DynamicWhiteHat/Arc/CAD/PCB/Freedom.kicad_sch

## KiCad design CAD/PCB/Freedom.kicad_sch (2026-02-23)

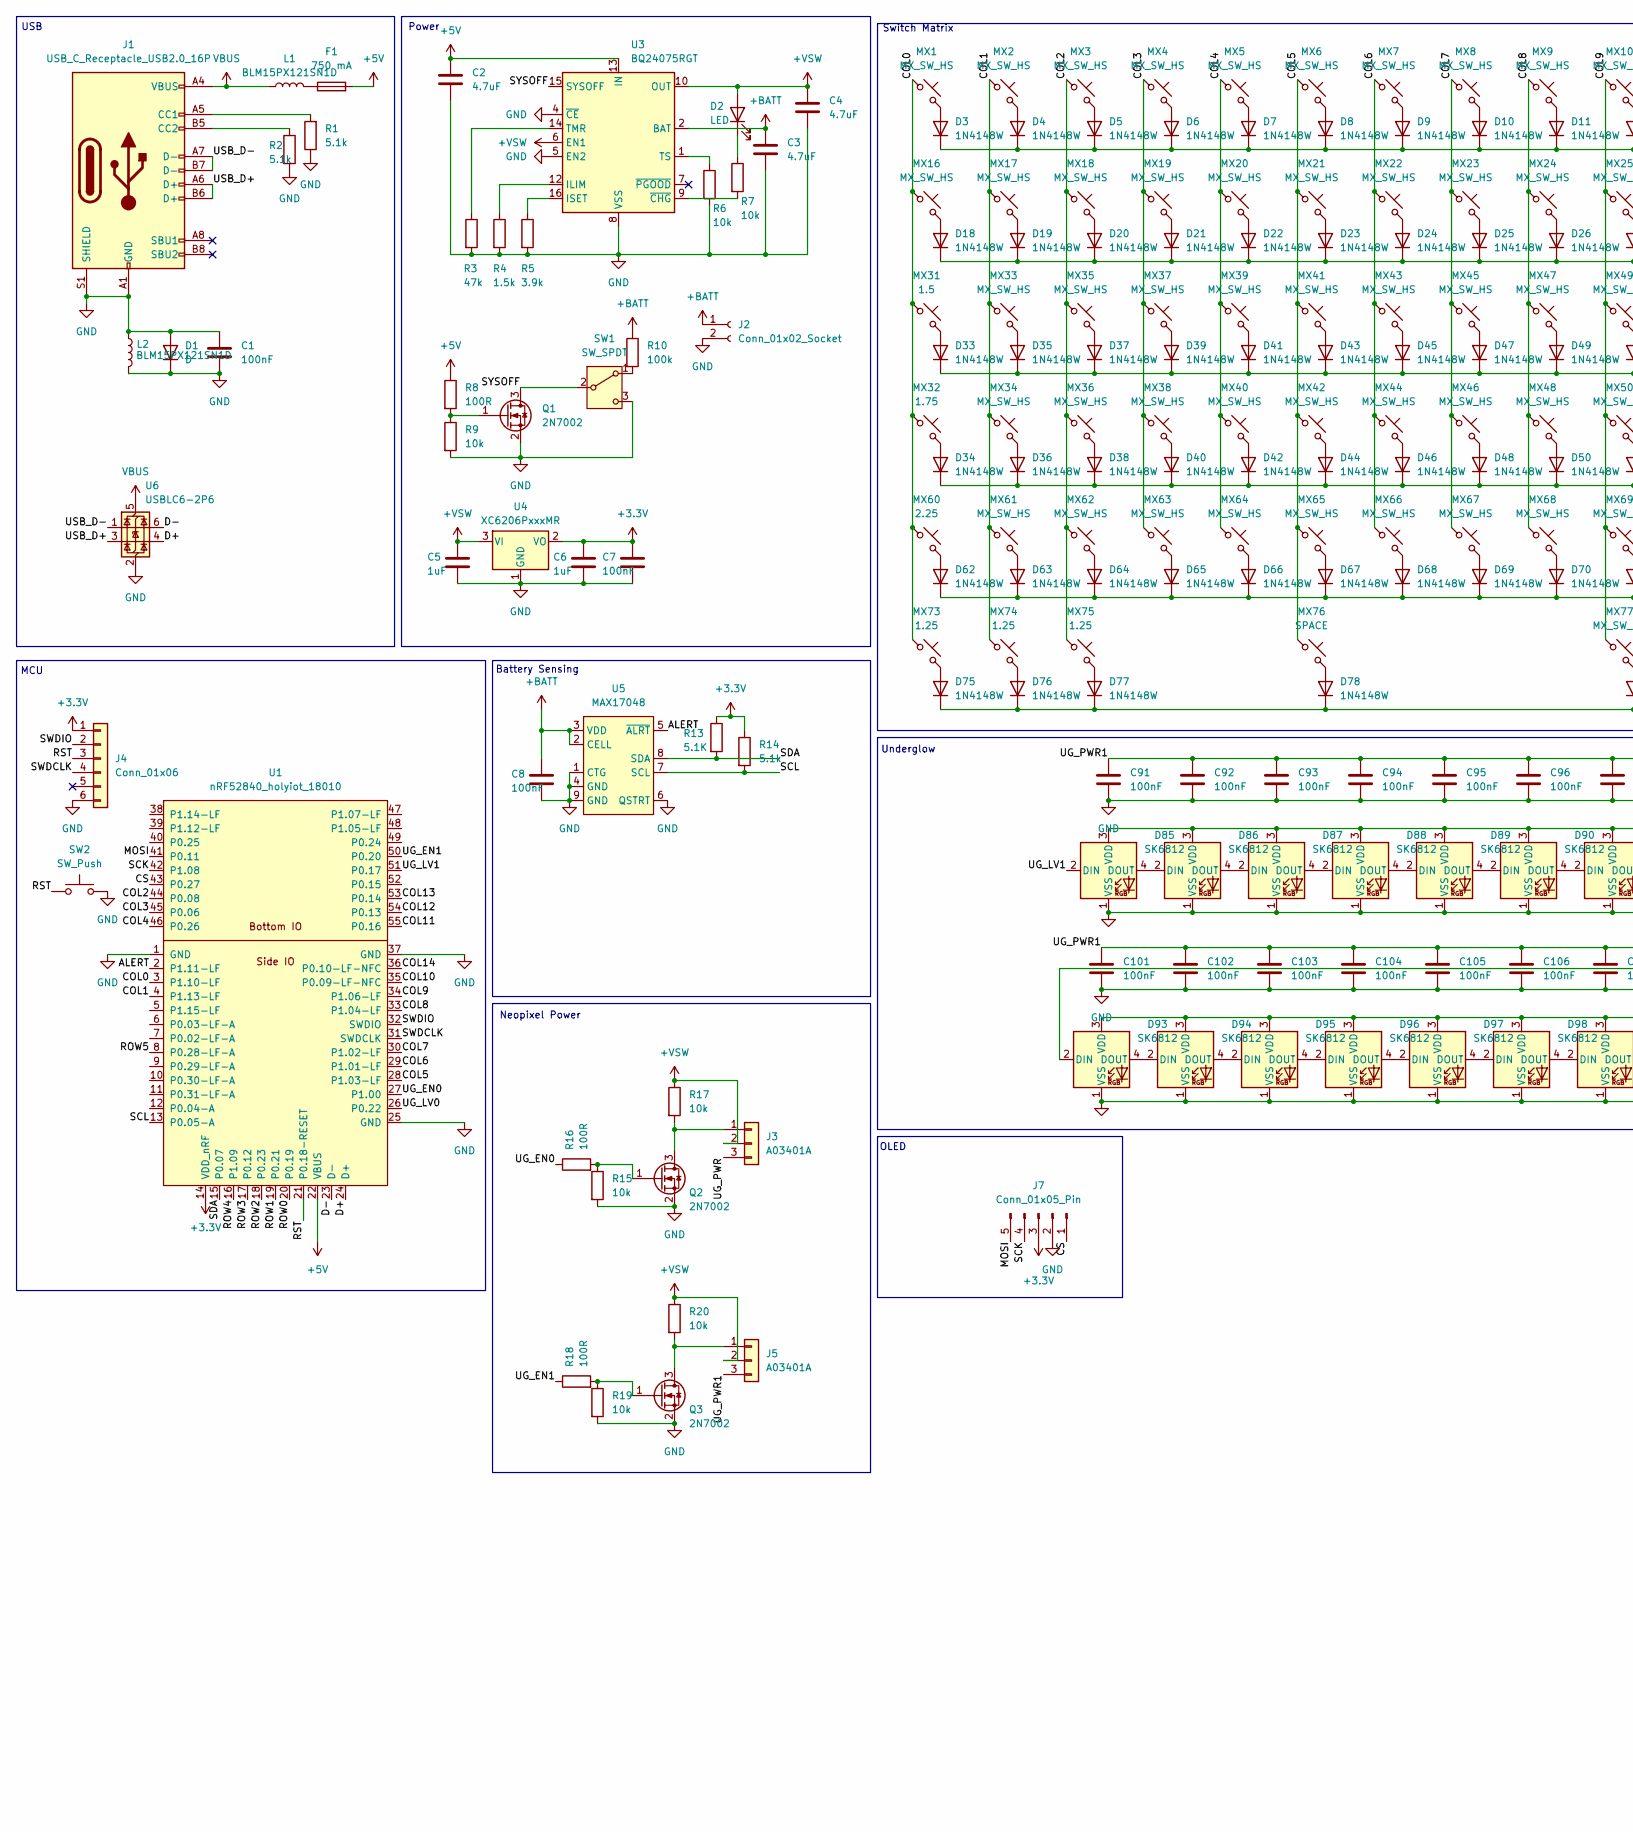
[picture p12: schematic Freedom.kicad_sch, part in row 1, column 1]

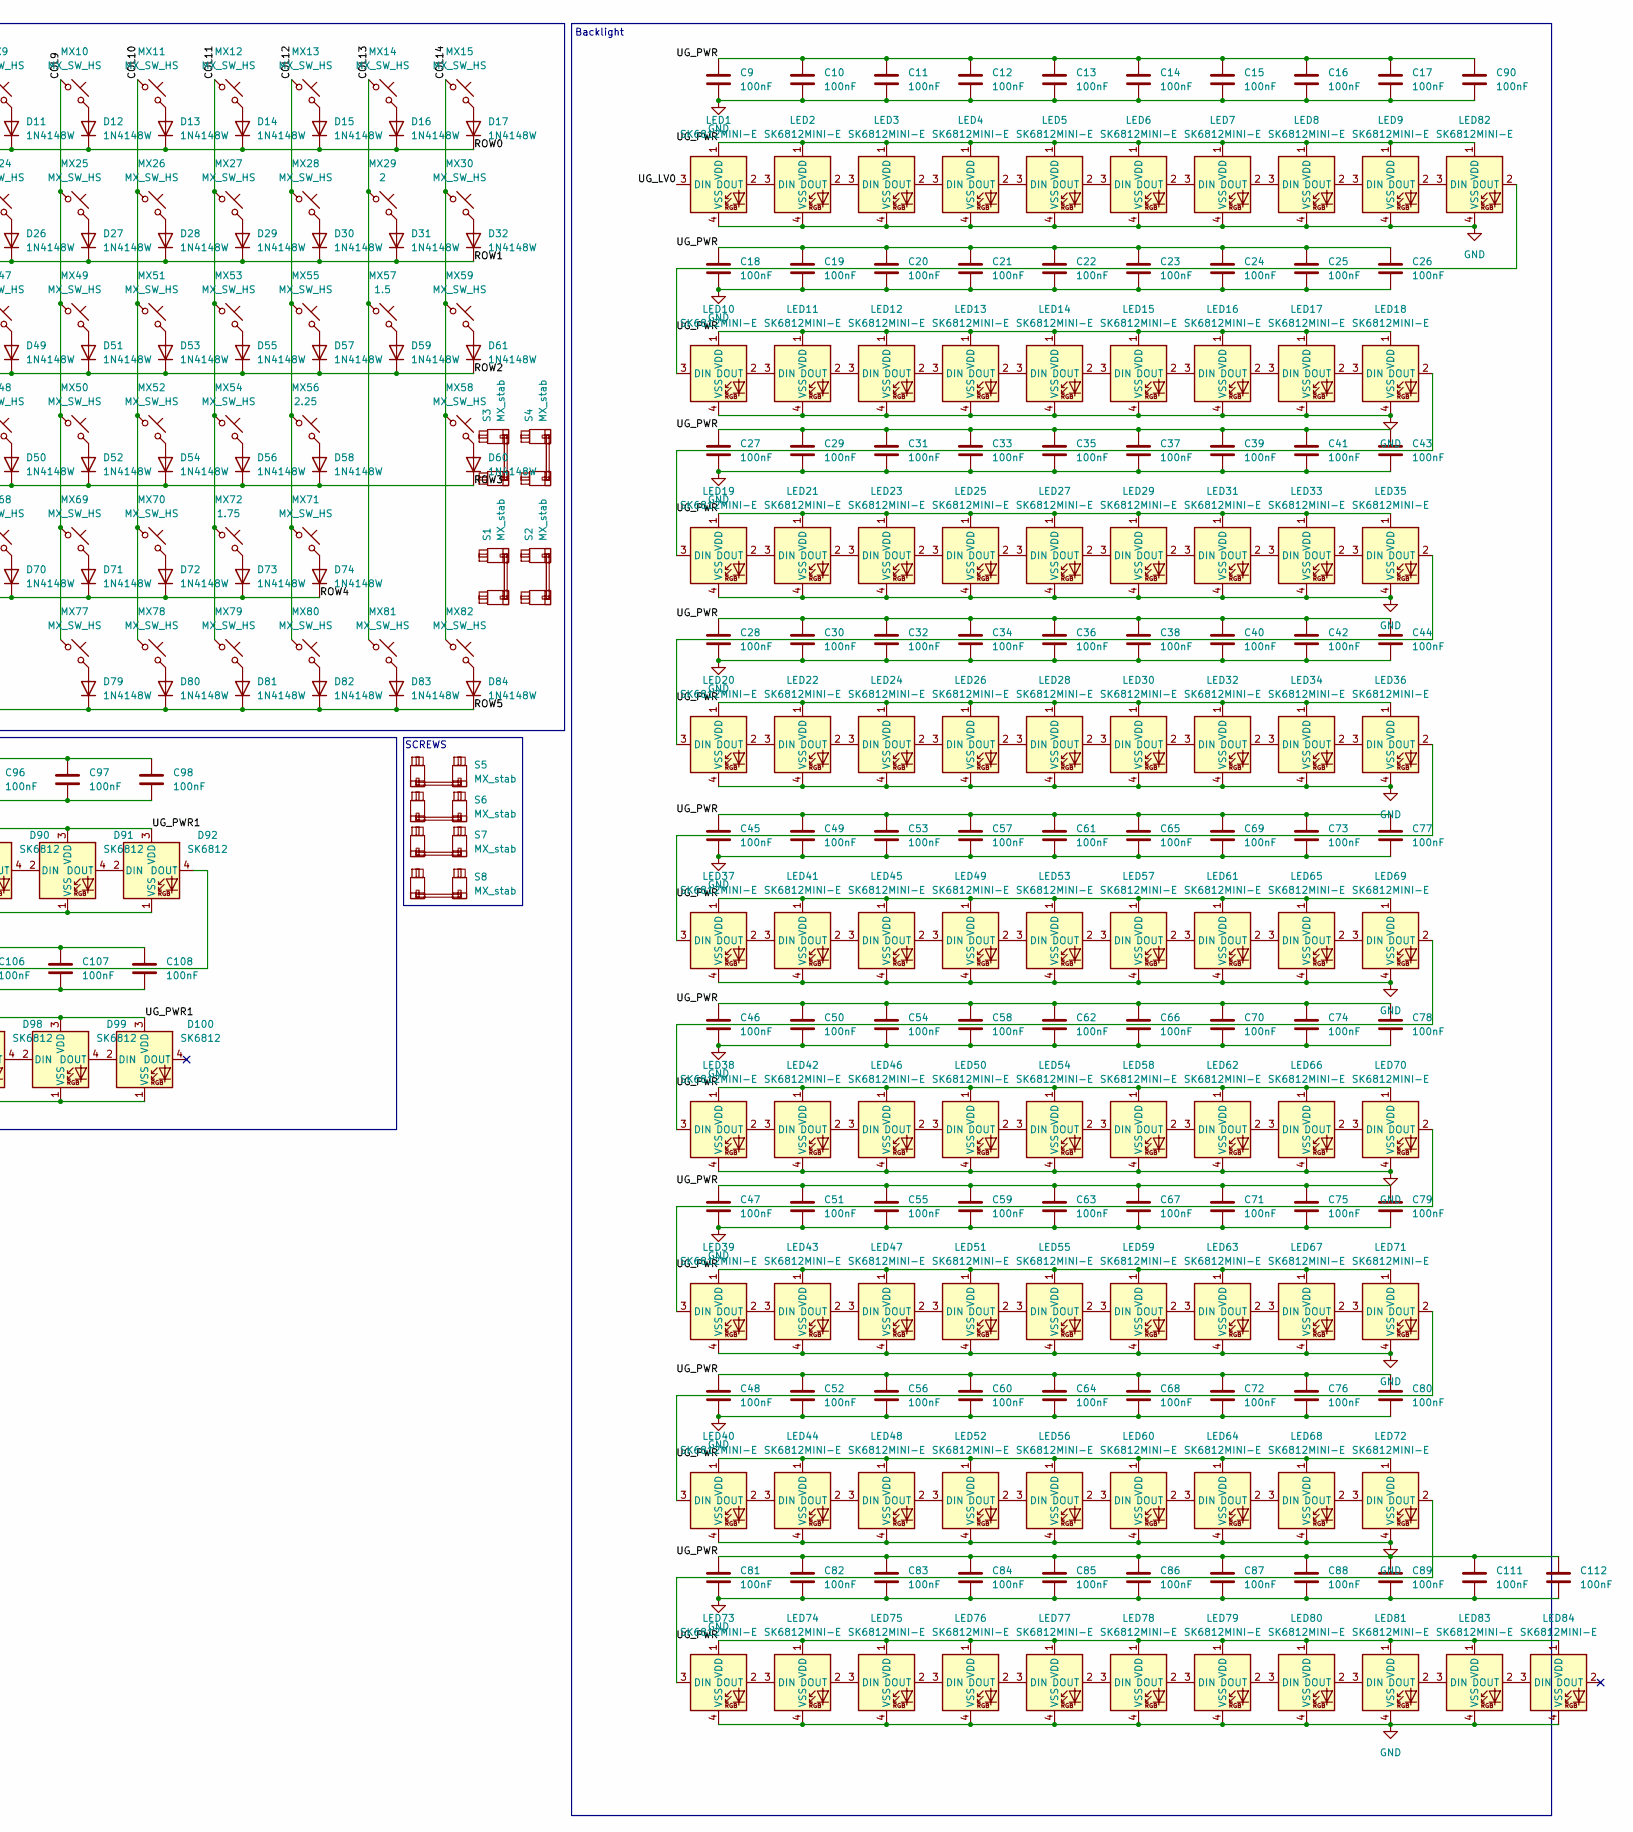
[picture p13: schematic Freedom.kicad_sch, part in row 1, column 2]

Parts:
C1, C7, C8, C9, C10, C11, C12, C13, C14, C15, C16, C17, C18, C19, C20, C21, C22, C23, C24, C25, C26, C27, C28, C29, C30, C31, C32, C33, C34, C35, C36, C37, C38, C39, C40, C41, C42, C43, C44, C45, C46, C47, C48, C49, C50, C51, C52, C53, C54, C55, C56, C57, C58, C59, C60, C61, C62, C63, C64, C65, C66, C67, C68, C69, C70, C71, C72, C73, C74, C75, C76, C77, C78, C79, C80, C81, C82, C83, C84, C85, C86, C87, C88, C89, C90, C91, C92, C93, C94, C95, C96, C97, C98, C101, C102, C103, C104, C105, C106, C107, C108, C111, C112: 100nF; C_0603_1608Metric
C2, C3, C4: 4.7uF; C_0603_1608Metric
C5, C6: 1uF; C_0603_1608Metric
D1: D; D_SOD-323
D2: LED; LED_0603_1608Metric
D3, D4, D5, D6, D7, D8, D9, D10, D11, D12, D13, D14, D15, D16, D17, D18, D19, D20, D21, D22, D23, D24, D25, D26, D27, D28, D29, D30, D31, D32, D33, D34, D35, D36, D37, D38, D39, D40, D41, D42, D43, D44, D45, D46, D47, D48, D49, D50, D51, D52, D53, D54, D55, D56, D57, D58, D59, D60, D61, D62, D63, D64, D65, D66, D67, D68, D69, D70, D71, D72, D73, D74, D75, D76, D77, D78, D79, D80, D81, D82, D83, D84: 1N4148W; D_SOD-123
D85, D86, D87, D88, D89, D90, D91, D92, D93, D94, D95, D96, D97, D98, D99, D100: SK6812; LED_SK6812MINI_PLCC4_3.5x3.5mm_P1.75mm
F1: 750 mA; Fuse_0603_1608Metric
J1: USB_C_Receptacle_USB2.0_16P; USB_C_Receptacle_HRO_TYPE-C-31-M-12
J2: Conn_01x02_Socket; JST_PH_S2B-PH-K_1x02_P2.00mm_Horizontal
J3, J5: A03401A; SOT-23
J4: Conn_01x06; PinHeader_1x06_P1.27mm_Vertical
J7: Conn_01x05_Pin; PinSocket_1x05_P2.54mm_Vertical
L1, L2: BLM15PX121SN1D; C_0402_1005Metric
LED1, LED2, LED3, LED4, LED5, LED6, LED7, LED8, LED9, LED10, LED11, LED12, LED13, LED14, LED15, LED16, LED17, LED18, LED19, LED20, LED21, LED22, LED23, LED24, LED25, LED26, LED27, LED28, LED29, LED30, LED31, LED32, LED33, LED34, LED35, LED36, LED37, LED38, LED39, LED40, LED41, LED42, LED43, LED44, LED45, LED46, LED47, LED48, LED49, LED50, LED51, LED52, LED53, LED54, LED55, LED56, LED57, LED58, LED59, LED60, LED61, LED62, LED63, LED64, LED65, LED66, LED67, LED68, LED69, LED70, LED71, LED72, LED73, LED74, LED75, LED76, LED77, LED78, LED79, LED80, LED81, LED82, LED83, LED84: SK6812MINI-E; LED_MX_6028R
MX1, MX2, MX3, MX4, MX5, MX6, MX7, MX8, MX9, MX10, MX11, MX12, MX13, MX14, MX15, MX16, MX17, MX18, MX19, MX20, MX21, MX22, MX23, MX24, MX25, MX26, MX27, MX28, MX30, MX33, MX34, MX35, MX36, MX37, MX38, MX39, MX40, MX41, MX42, MX43, MX44, MX45, MX46, MX47, MX48, MX49, MX50, MX51, MX52, MX53, MX54, MX55, MX58, MX59, MX61, MX62, MX63, MX64, MX65, MX66, MX67, MX68, MX69, MX70, MX71, MX77, MX78, MX79, MX80, MX81, MX82: MX_SW_HS; SW_MX_HS_CPG151101S11_1u
MX29: 2; SW_MX_HS_CPG151101S11_2u
MX31, MX57: 1.5; SW_MX_HS_CPG151101S11_1.5u
MX32, MX72: 1.75; SW_MX_HS_CPG151101S11_1.75u
MX56, MX60: 2.25; SW_MX_HS_CPG151101S11_2.25u
MX73, MX74, MX75: 1.25; SW_MX_HS_CPG151101S11_1.25u
MX76: SPACE; SW_MX_HS_CPG151101S11_6u
Q1, Q2, Q3: 2N7002; SOT-23
R1, R2, R14: 5.1k; R_0603_1608Metric
R3: 47k; R_0603_1608Metric
R4: 1.5k; R_0603_1608Metric
R5: 3.9k; R_0603_1608Metric
R6, R7, R9, R15, R17, R19, R20: 10k; R_0603_1608Metric
R8, R16, R18: 100R; R_0603_1608Metric
R10: 100k; R_0603_1608Metric
R13: 5.1K; R_0603_1608Metric
S1: MX_stab; STAB_MX_P_6.25u
S2, S4: MX_stab; STAB_MX_2.25u
S3: MX_stab; STAB_MX_2u
S5, S6, S7, S8: MX_stab; MountingHole_2.2mm_M2
SW1: SW_SPDT; SW_SSSS811101
SW2: SW_Push; SW_TS-1088-AR02016
U1: nRF52840_holyiot_18010
U3: BQ24075RGT; VQFN-16-1EP_3x3mm_P0.5mm_EP1.6x1.6mm
U4: XC6206PxxxMR; SOT-23-3
U5: MAX17048; DFN-8-1EP_2x2mm_P0.5mm_EP0.8x1.6mm
U6: USBLC6-2P6; SOT-666

Connections:
+3.3V: C6.1, C7.1, J4.1, J7.3, R13.1, R14.1, U1.14 (VDD_nRF), U4.2 (VO)
+5V: C2.1, F1.2, R8.1, U1.22 (VBUS), U3.13 (IN)
+BATT: C3.1, C8.1, J2.1, R10.1, U3.2 (BAT), U3.3 (BAT), U5.2 (CELL), U5.3 (VDD)
+VSW: C4.1, C5.1, D2.2 (A), J3.2, J5.2, R17.1, R20.1, U3.6 (EN1), U3.10 (OUT), U3.11 (OUT), U4.3 (VI)
ALERT: U1.2 (P1.11-LF), U5.5 (~ALRT)
COL0: MX1.1, MX16.1, MX31.1, MX32.1, MX60.1, MX73.1, U1.3 (P1.10-LF)
COL1: MX2.1, MX17.1, MX33.1, MX34.1, MX61.1, MX74.1, U1.4 (P1.13-LF)
COL2: MX3.1, MX18.1, MX35.1, MX36.1, MX62.1, MX75.1, U1.44 (P0.08)
COL3: MX4.1, MX19.1, MX37.1, MX38.1, MX63.1, U1.45 (P0.06)
COL4: MX5.1, MX20.1, MX39.1, MX40.1, MX64.1, U1.46 (P0.26)
COL5: MX6.1, MX21.1, MX41.1, MX42.1, MX65.1, MX76.1, U1.28 (P1.03-LF)
COL6: MX7.1, MX22.1, MX43.1, MX44.1, MX66.1, U1.29 (P1.01-LF)
COL7: MX8.1, MX23.1, MX45.1, MX46.1, MX67.1, U1.30 (P1.02-LF)
COL8: MX9.1, MX24.1, MX47.1, MX48.1, MX68.1, U1.33 (P1.04-LF)
COL9: MX10.1, MX25.1, MX49.1, MX50.1, MX69.1, MX77.1, U1.34 (P1.06-LF)
COL10: MX11.1, MX26.1, MX51.1, MX52.1, MX70.1, MX78.1, U1.35 (P0.09-LF-NFC)
COL11: MX12.1, MX27.1, MX53.1, MX54.1, MX72.1, MX79.1, U1.55 (P0.16)
COL12: MX13.1, MX28.1, MX55.1, MX56.1, MX71.1, MX80.1, U1.54 (P0.13)
COL13: MX14.1, MX29.1, MX57.1, MX81.1, U1.53 (P0.14)
COL14: MX15.1, MX30.1, MX58.1, MX59.1, MX82.1, U1.36 (P0.10-LF-NFC)
CS: J7.1, U1.43 (P0.27)
D+: U1.24 (D+), U6.4 (I/O2)
D-: U1.23 (D-), U6.6 (I/O1)
GND: C1.1, C1.2, C2.2, C3.2, C4.2, C5.2, C6.2, C7.2, C8.2, C9.2, C10.2, C11.2, C12.2, C13.2, C14.2, C15.2, C16.2, C17.2, C18.2, C19.2, C20.2, C21.2, C22.2, C23.2, C24.2, C25.2, C26.2, C27.2, C28.2, C29.2, C30.2, C31.2, C32.2, C33.2, C34.2, C35.2, C36.2, C37.2, C38.2, C39.2, C40.2, C41.2, C42.2, C43.2, C44.2, C45.2, C46.2, C47.2, C48.2, C49.2, C50.2, C51.2, C52.2, C53.2, C54.2, C55.2, C56.2, C57.2, C58.2, C59.2, C60.2, C61.2, C62.2, C63.2, C64.2, C65.2, C66.2, C67.2, C68.2, C69.2, C70.2, C71.2, C72.2, C73.2, C74.2, C75.2, C76.2, C77.2, C78.2, C79.2, C80.2, C81.2, C82.2, C83.2, C84.2, C85.2, C86.2, C87.2, C88.2, C89.2, C90.2, C91.2, C92.2, C93.2, C94.2, C95.2, C96.2, C97.2, C98.2, C101.2, C102.2, C103.2, C104.2, C105.2, C106.2, C107.2, C108.2, C111.2, C112.2, D1.1 (K), D1.2 (A), D85.1 (VSS), D86.1 (VSS), D87.1 (VSS), D88.1 (VSS), D89.1 (VSS), D90.1 (VSS), D91.1 (VSS), D92.1 (VSS), D93.1 (VSS), D94.1 (VSS), D95.1 (VSS), D96.1 (VSS), D97.1 (VSS), D98.1 (VSS), D99.1 (VSS), D100.1 (VSS), J1.A1 (GND), J1.A12 (GND), J1.B1 (GND), J1.B12 (GND), J1.S1 (SHIELD), J2.2, J4.6, J7.2, L2.1, L2.2, LED1.4 (VSS), LED2.4 (VSS), LED3.4 (VSS), LED4.4 (VSS), LED5.4 (VSS), LED6.4 (VSS), LED7.4 (VSS), LED8.4 (VSS), LED9.4 (VSS), LED10.4 (VSS), LED11.4 (VSS), LED12.4 (VSS), LED13.4 (VSS), LED14.4 (VSS), LED15.4 (VSS), LED16.4 (VSS), LED17.4 (VSS), LED18.4 (VSS), LED19.4 (VSS), LED20.4 (VSS), LED21.4 (VSS), LED22.4 (VSS), LED23.4 (VSS), LED24.4 (VSS), LED25.4 (VSS), LED26.4 (VSS), LED27.4 (VSS), LED28.4 (VSS), LED29.4 (VSS), LED30.4 (VSS), LED31.4 (VSS), LED32.4 (VSS), LED33.4 (VSS), LED34.4 (VSS), LED35.4 (VSS), LED36.4 (VSS), LED37.4 (VSS), LED38.4 (VSS), LED39.4 (VSS), LED40.4 (VSS), LED41.4 (VSS), LED42.4 (VSS), LED43.4 (VSS), LED44.4 (VSS), LED45.4 (VSS), LED46.4 (VSS), LED47.4 (VSS), LED48.4 (VSS), LED49.4 (VSS), LED50.4 (VSS), LED51.4 (VSS), LED52.4 (VSS), LED53.4 (VSS), LED54.4 (VSS), LED55.4 (VSS), LED56.4 (VSS), LED57.4 (VSS), LED58.4 (VSS), LED59.4 (VSS), LED60.4 (VSS), LED61.4 (VSS), LED62.4 (VSS), LED63.4 (VSS), LED64.4 (VSS), LED65.4 (VSS), LED66.4 (VSS), LED67.4 (VSS), LED68.4 (VSS), LED69.4 (VSS), LED70.4 (VSS), LED71.4 (VSS), LED72.4 (VSS), LED73.4 (VSS), LED74.4 (VSS), LED75.4 (VSS), LED76.4 (VSS), LED77.4 (VSS), LED78.4 (VSS), LED79.4 (VSS), LED80.4 (VSS), LED81.4 (VSS), LED82.4 (VSS), LED83.4 (VSS), LED84.4 (VSS), Q1.2 (S), Q2.2 (S), Q3.2 (S), R1.1, R2.2, R3.2, R4.2, R5.2, R6.2, R9.2, R15.2, R19.2, SW1.3 (C), SW2.2, U1.1 (GND), U1.25 (GND), U1.37 (GND), U3.4 (~CE), U3.5 (EN2), U3.8 (VSS), U3.17 (VSS), U4.1 (GND), U5.1 (CTG), U5.4 (GND), U5.6 (QSTRT), U5.9 (GND), U6.2 (GND)
MOSI: J7.5, U1.41 (P0.11)
unnamed: D2.1 (K), R7.1
unnamed: D3.2 (A), MX1.2
unnamed: D4.2 (A), MX2.2
unnamed: D5.2 (A), MX3.2
unnamed: D6.2 (A), MX4.2
unnamed: D7.2 (A), MX5.2
unnamed: D8.2 (A), MX6.2
unnamed: D9.2 (A), MX7.2
unnamed: D10.2 (A), MX8.2
unnamed: D11.2 (A), MX9.2
unnamed: D12.2 (A), MX10.2
unnamed: D13.2 (A), MX11.2
unnamed: D14.2 (A), MX12.2
unnamed: D15.2 (A), MX13.2
unnamed: D16.2 (A), MX14.2
unnamed: D17.2 (A), MX15.2
unnamed: D18.2 (A), MX16.2
unnamed: D19.2 (A), MX17.2
unnamed: D20.2 (A), MX18.2
unnamed: D21.2 (A), MX19.2
unnamed: D22.2 (A), MX20.2
unnamed: D23.2 (A), MX21.2
unnamed: D24.2 (A), MX22.2
unnamed: D25.2 (A), MX23.2
unnamed: D26.2 (A), MX24.2
unnamed: D27.2 (A), MX25.2
unnamed: D28.2 (A), MX26.2
unnamed: D29.2 (A), MX27.2
unnamed: D30.2 (A), MX28.2
unnamed: D31.2 (A), MX29.2
unnamed: D32.2 (A), MX30.2
unnamed: D33.2 (A), MX31.2
unnamed: D34.2 (A), MX32.2
unnamed: D35.2 (A), MX33.2
unnamed: D36.2 (A), MX34.2
unnamed: D37.2 (A), MX35.2
unnamed: D38.2 (A), MX36.2
unnamed: D39.2 (A), MX37.2
unnamed: D40.2 (A), MX38.2
unnamed: D41.2 (A), MX39.2
unnamed: D42.2 (A), MX40.2
unnamed: D43.2 (A), MX41.2
unnamed: D44.2 (A), MX42.2
unnamed: D45.2 (A), MX43.2
unnamed: D46.2 (A), MX44.2
unnamed: D47.2 (A), MX45.2
unnamed: D48.2 (A), MX46.2
unnamed: D49.2 (A), MX47.2
unnamed: D50.2 (A), MX48.2
unnamed: D51.2 (A), MX49.2
unnamed: D52.2 (A), MX50.2
unnamed: D53.2 (A), MX51.2
unnamed: D54.2 (A), MX52.2
unnamed: D55.2 (A), MX53.2
unnamed: D56.2 (A), MX54.2
unnamed: D57.2 (A), MX55.2
unnamed: D58.2 (A), MX56.2
unnamed: D59.2 (A), MX57.2
unnamed: D60.2 (A), MX58.2
unnamed: D61.2 (A), MX59.2
unnamed: D62.2 (A), MX60.2
unnamed: D63.2 (A), MX61.2
unnamed: D64.2 (A), MX62.2
unnamed: D65.2 (A), MX63.2
unnamed: D66.2 (A), MX64.2
unnamed: D67.2 (A), MX65.2
unnamed: D68.2 (A), MX66.2
unnamed: D69.2 (A), MX67.2
unnamed: D70.2 (A), MX68.2
unnamed: D71.2 (A), MX69.2
unnamed: D72.2 (A), MX70.2
unnamed: D73.2 (A), MX72.2
unnamed: D74.2 (A), MX71.2
unnamed: D75.2 (A), MX73.2
unnamed: D76.2 (A), MX74.2
unnamed: D77.2 (A), MX75.2
unnamed: D78.2 (A), MX76.2
unnamed: D79.2 (A), MX77.2
unnamed: D80.2 (A), MX78.2
unnamed: D81.2 (A), MX79.2
unnamed: D82.2 (A), MX80.2
unnamed: D83.2 (A), MX81.2
unnamed: D84.2 (A), MX82.2
unnamed: D85.4 (DOUT), D86.2 (DIN)
unnamed: D86.4 (DOUT), D87.2 (DIN)
unnamed: D87.4 (DOUT), D88.2 (DIN)
unnamed: D88.4 (DOUT), D89.2 (DIN)
unnamed: D89.4 (DOUT), D90.2 (DIN)
unnamed: D90.4 (DOUT), D91.2 (DIN)
unnamed: D91.4 (DOUT), D92.2 (DIN)
unnamed: D92.4 (DOUT), D93.2 (DIN)
unnamed: D93.4 (DOUT), D94.2 (DIN)
unnamed: D94.4 (DOUT), D95.2 (DIN)
unnamed: D95.4 (DOUT), D96.2 (DIN)
unnamed: D96.4 (DOUT), D97.2 (DIN)
unnamed: D97.4 (DOUT), D98.2 (DIN)
unnamed: D98.4 (DOUT), D99.2 (DIN)
unnamed: D99.4 (DOUT), D100.2 (DIN)
unnamed: F1.1, L1.2
unnamed: J1.A5 (CC1), R1.2
unnamed: J1.B5 (CC2), R2.1
unnamed: J3.1, Q2.3 (D), R17.2
unnamed: J5.1, Q3.3 (D), R20.2
unnamed: LED1.2 (DOUT), LED2.3 (DIN)
unnamed: LED2.2 (DOUT), LED3.3 (DIN)
unnamed: LED3.2 (DOUT), LED4.3 (DIN)
unnamed: LED4.2 (DOUT), LED5.3 (DIN)
unnamed: LED5.2 (DOUT), LED6.3 (DIN)
unnamed: LED6.2 (DOUT), LED7.3 (DIN)
unnamed: LED7.2 (DOUT), LED8.3 (DIN)
unnamed: LED8.2 (DOUT), LED9.3 (DIN)
unnamed: LED10.2 (DOUT), LED11.3 (DIN)
unnamed: LED10.3 (DIN), LED82.2 (DOUT)
unnamed: LED11.2 (DOUT), LED12.3 (DIN)
unnamed: LED12.2 (DOUT), LED13.3 (DIN)
unnamed: LED13.2 (DOUT), LED14.3 (DIN)
unnamed: LED14.2 (DOUT), LED15.3 (DIN)
unnamed: LED15.2 (DOUT), LED16.3 (DIN)
unnamed: LED16.2 (DOUT), LED17.3 (DIN)
unnamed: LED17.2 (DOUT), LED18.3 (DIN)
unnamed: LED18.2 (DOUT), LED19.3 (DIN)
unnamed: LED19.2 (DOUT), LED21.3 (DIN)
unnamed: LED20.2 (DOUT), LED22.3 (DIN)
unnamed: LED20.3 (DIN), LED35.2 (DOUT)
unnamed: LED21.2 (DOUT), LED23.3 (DIN)
unnamed: LED22.2 (DOUT), LED24.3 (DIN)
unnamed: LED23.2 (DOUT), LED25.3 (DIN)
unnamed: LED24.2 (DOUT), LED26.3 (DIN)
unnamed: LED25.2 (DOUT), LED27.3 (DIN)
unnamed: LED26.2 (DOUT), LED28.3 (DIN)
unnamed: LED27.2 (DOUT), LED29.3 (DIN)
unnamed: LED28.2 (DOUT), LED30.3 (DIN)
unnamed: LED29.2 (DOUT), LED31.3 (DIN)
unnamed: LED30.2 (DOUT), LED32.3 (DIN)
unnamed: LED31.2 (DOUT), LED33.3 (DIN)
unnamed: LED32.2 (DOUT), LED34.3 (DIN)
unnamed: LED33.2 (DOUT), LED35.3 (DIN)
unnamed: LED34.2 (DOUT), LED36.3 (DIN)
unnamed: LED36.2 (DOUT), LED37.3 (DIN)
unnamed: LED37.2 (DOUT), LED41.3 (DIN)
unnamed: LED38.2 (DOUT), LED42.3 (DIN)
unnamed: LED38.3 (DIN), LED69.2 (DOUT)
unnamed: LED39.2 (DOUT), LED43.3 (DIN)
unnamed: LED39.3 (DIN), LED70.2 (DOUT)
unnamed: LED40.2 (DOUT), LED44.3 (DIN)
unnamed: LED40.3 (DIN), LED71.2 (DOUT)
unnamed: LED41.2 (DOUT), LED45.3 (DIN)
unnamed: LED42.2 (DOUT), LED46.3 (DIN)
unnamed: LED43.2 (DOUT), LED47.3 (DIN)
unnamed: LED44.2 (DOUT), LED48.3 (DIN)
unnamed: LED45.2 (DOUT), LED49.3 (DIN)
unnamed: LED46.2 (DOUT), LED50.3 (DIN)
unnamed: LED47.2 (DOUT), LED51.3 (DIN)
unnamed: LED48.2 (DOUT), LED52.3 (DIN)
unnamed: LED49.2 (DOUT), LED53.3 (DIN)
unnamed: LED50.2 (DOUT), LED54.3 (DIN)
unnamed: LED51.2 (DOUT), LED55.3 (DIN)
unnamed: LED52.2 (DOUT), LED56.3 (DIN)
unnamed: LED53.2 (DOUT), LED57.3 (DIN)
unnamed: LED54.2 (DOUT), LED58.3 (DIN)
unnamed: LED55.2 (DOUT), LED59.3 (DIN)
unnamed: LED56.2 (DOUT), LED60.3 (DIN)
unnamed: LED57.2 (DOUT), LED61.3 (DIN)
unnamed: LED58.2 (DOUT), LED62.3 (DIN)
unnamed: LED59.2 (DOUT), LED63.3 (DIN)
unnamed: LED60.2 (DOUT), LED64.3 (DIN)
unnamed: LED61.2 (DOUT), LED65.3 (DIN)
unnamed: LED62.2 (DOUT), LED66.3 (DIN)
unnamed: LED63.2 (DOUT), LED67.3 (DIN)
unnamed: LED64.2 (DOUT), LED68.3 (DIN)
unnamed: LED65.2 (DOUT), LED69.3 (DIN)
unnamed: LED66.2 (DOUT), LED70.3 (DIN)
unnamed: LED67.2 (DOUT), LED71.3 (DIN)
unnamed: LED68.2 (DOUT), LED72.3 (DIN)
unnamed: LED72.2 (DOUT), LED73.3 (DIN)
unnamed: LED73.2 (DOUT), LED74.3 (DIN)
unnamed: LED74.2 (DOUT), LED75.3 (DIN)
unnamed: LED75.2 (DOUT), LED76.3 (DIN)
unnamed: LED76.2 (DOUT), LED77.3 (DIN)
unnamed: LED77.2 (DOUT), LED78.3 (DIN)
unnamed: LED78.2 (DOUT), LED79.3 (DIN)
unnamed: LED79.2 (DOUT), LED80.3 (DIN)
unnamed: LED80.2 (DOUT), LED81.3 (DIN)
unnamed: LED81.2 (DOUT), LED83.3 (DIN)
unnamed: LED9.2 (DOUT), LED82.3 (DIN)
unnamed: LED83.2 (DOUT), LED84.3 (DIN)
unnamed: Q1.1 (G), R8.2, R9.1
unnamed: Q2.1 (G), R15.1, R16.2
unnamed: Q3.1 (G), R18.2, R19.1
unnamed: R3.1, U3.14 (TMR)
unnamed: R4.1, U3.12 (ILIM)
unnamed: R5.1, U3.16 (ISET)
unnamed: R6.1, U3.1 (TS)
unnamed: R7.2, U3.9 (~CHG)
unnamed: R10.2, SW1.1 (A)
ROW0: D3.1 (K), D4.1 (K), D5.1 (K), D6.1 (K), D7.1 (K), D8.1 (K), D9.1 (K), D10.1 (K), D11.1 (K), D12.1 (K), D13.1 (K), D14.1 (K), D15.1 (K), D16.1 (K), D17.1 (K), U1.20 (P0.19)
ROW1: D18.1 (K), D19.1 (K), D20.1 (K), D21.1 (K), D22.1 (K), D23.1 (K), D24.1 (K), D25.1 (K), D26.1 (K), D27.1 (K), D28.1 (K), D29.1 (K), D30.1 (K), D31.1 (K), D32.1 (K), U1.19 (P0.21)
ROW2: D33.1 (K), D35.1 (K), D37.1 (K), D39.1 (K), D41.1 (K), D43.1 (K), D45.1 (K), D47.1 (K), D49.1 (K), D51.1 (K), D53.1 (K), D55.1 (K), D57.1 (K), D59.1 (K), D61.1 (K), U1.18 (P0.23)
ROW3: D34.1 (K), D36.1 (K), D38.1 (K), D40.1 (K), D42.1 (K), D44.1 (K), D46.1 (K), D48.1 (K), D50.1 (K), D52.1 (K), D54.1 (K), D56.1 (K), D58.1 (K), D60.1 (K), U1.17 (P0.12)
ROW4: D62.1 (K), D63.1 (K), D64.1 (K), D65.1 (K), D66.1 (K), D67.1 (K), D68.1 (K), D69.1 (K), D70.1 (K), D71.1 (K), D72.1 (K), D73.1 (K), D74.1 (K), U1.16 (P1.09)
ROW5: D75.1 (K), D76.1 (K), D77.1 (K), D78.1 (K), D79.1 (K), D80.1 (K), D81.1 (K), D82.1 (K), D83.1 (K), D84.1 (K), U1.8 (P0.28-LF-A)
RST: J4.3, SW2.1, U1.21 (P0.18-RESET)
SCK: J7.4, U1.42 (P1.08)
SCL: R14.2, U1.13 (P0.05-A), U5.7 (SCL)
SDA: R13.2, U1.15 (P0.07), U5.8 (SDA)
SWDCLK: J4.4, U1.31 (SWDCLK)
SWDIO: J4.2, U1.32 (SWDIO)
SYSOFF: Q1.3 (D), SW1.2 (B), U3.15 (SYSOFF)
UG_EN0: R16.1, U1.27 (P1.00)
UG_EN1: R18.1, U1.50 (P0.20)
UG_LV0: LED1.3 (DIN), U1.26 (P0.22)
UG_LV1: D85.2 (DIN), U1.51 (P0.17)
UG_PWR: C9.1, C10.1, C11.1, C12.1, C13.1, C14.1, C15.1, C16.1, C17.1, C18.1, C19.1, C20.1, C21.1, C22.1, C23.1, C24.1, C25.1, C26.1, C27.1, C28.1, C29.1, C30.1, C31.1, C32.1, C33.1, C34.1, C35.1, C36.1, C37.1, C38.1, C39.1, C40.1, C41.1, C42.1, C43.1, C44.1, C45.1, C46.1, C47.1, C48.1, C49.1, C50.1, C51.1, C52.1, C53.1, C54.1, C55.1, C56.1, C57.1, C58.1, C59.1, C60.1, C61.1, C62.1, C63.1, C64.1, C65.1, C66.1, C67.1, C68.1, C69.1, C70.1, C71.1, C72.1, C73.1, C74.1, C75.1, C76.1, C77.1, C78.1, C79.1, C80.1, C81.1, C82.1, C83.1, C84.1, C85.1, C86.1, C87.1, C88.1, C89.1, C90.1, C111.1, C112.1, J3.3, LED1.1 (VDD), LED2.1 (VDD), LED3.1 (VDD), LED4.1 (VDD), LED5.1 (VDD), LED6.1 (VDD), LED7.1 (VDD), LED8.1 (VDD), LED9.1 (VDD), LED10.1 (VDD), LED11.1 (VDD), LED12.1 (VDD), LED13.1 (VDD), LED14.1 (VDD), LED15.1 (VDD), LED16.1 (VDD), LED17.1 (VDD), LED18.1 (VDD), LED19.1 (VDD), LED20.1 (VDD), LED21.1 (VDD), LED22.1 (VDD), LED23.1 (VDD), LED24.1 (VDD), LED25.1 (VDD), LED26.1 (VDD), LED27.1 (VDD), LED28.1 (VDD), LED29.1 (VDD), LED30.1 (VDD), LED31.1 (VDD), LED32.1 (VDD), LED33.1 (VDD), LED34.1 (VDD), LED35.1 (VDD), LED36.1 (VDD), LED37.1 (VDD), LED38.1 (VDD), LED39.1 (VDD), LED40.1 (VDD), LED41.1 (VDD), LED42.1 (VDD), LED43.1 (VDD), LED44.1 (VDD), LED45.1 (VDD), LED46.1 (VDD), LED47.1 (VDD), LED48.1 (VDD), LED49.1 (VDD), LED50.1 (VDD), LED51.1 (VDD), LED52.1 (VDD), LED53.1 (VDD), LED54.1 (VDD), LED55.1 (VDD), LED56.1 (VDD), LED57.1 (VDD), LED58.1 (VDD), LED59.1 (VDD), LED60.1 (VDD), LED61.1 (VDD), LED62.1 (VDD), LED63.1 (VDD), LED64.1 (VDD), LED65.1 (VDD), LED66.1 (VDD), LED67.1 (VDD), LED68.1 (VDD), LED69.1 (VDD), LED70.1 (VDD), LED71.1 (VDD), LED72.1 (VDD), LED73.1 (VDD), LED74.1 (VDD), LED75.1 (VDD), LED76.1 (VDD), LED77.1 (VDD), LED78.1 (VDD), LED79.1 (VDD), LED80.1 (VDD), LED81.1 (VDD), LED82.1 (VDD), LED83.1 (VDD), LED84.1 (VDD)
UG_PWR1: C91.1, C92.1, C93.1, C94.1, C95.1, C96.1, C97.1, C98.1, C101.1, C102.1, C103.1, C104.1, C105.1, C106.1, C107.1, C108.1, D85.3 (VDD), D86.3 (VDD), D87.3 (VDD), D88.3 (VDD), D89.3 (VDD), D90.3 (VDD), D91.3 (VDD), D92.3 (VDD), D93.3 (VDD), D94.3 (VDD), D95.3 (VDD), D96.3 (VDD), D97.3 (VDD), D98.3 (VDD), D99.3 (VDD), D100.3 (VDD), J5.3
USB_D+: J1.A6 (D+), J1.B6 (D+), U6.3 (I/O2)
USB_D-: J1.A7 (D-), J1.B7 (D-), U6.1 (I/O1)
VBUS: J1.A4 (VBUS), J1.A9 (VBUS), J1.B4 (VBUS), J1.B9 (VBUS), L1.1, U6.5 (VBUS)

Notes on the sheet:
Neopixel Power
Power
Switch Matrix
Battery Sensing
OLED
SCREWS
Underglow
Backlight
MCU
USB
